satshakit/satshakit-M7/media/satshakit-M7-clock-config.png

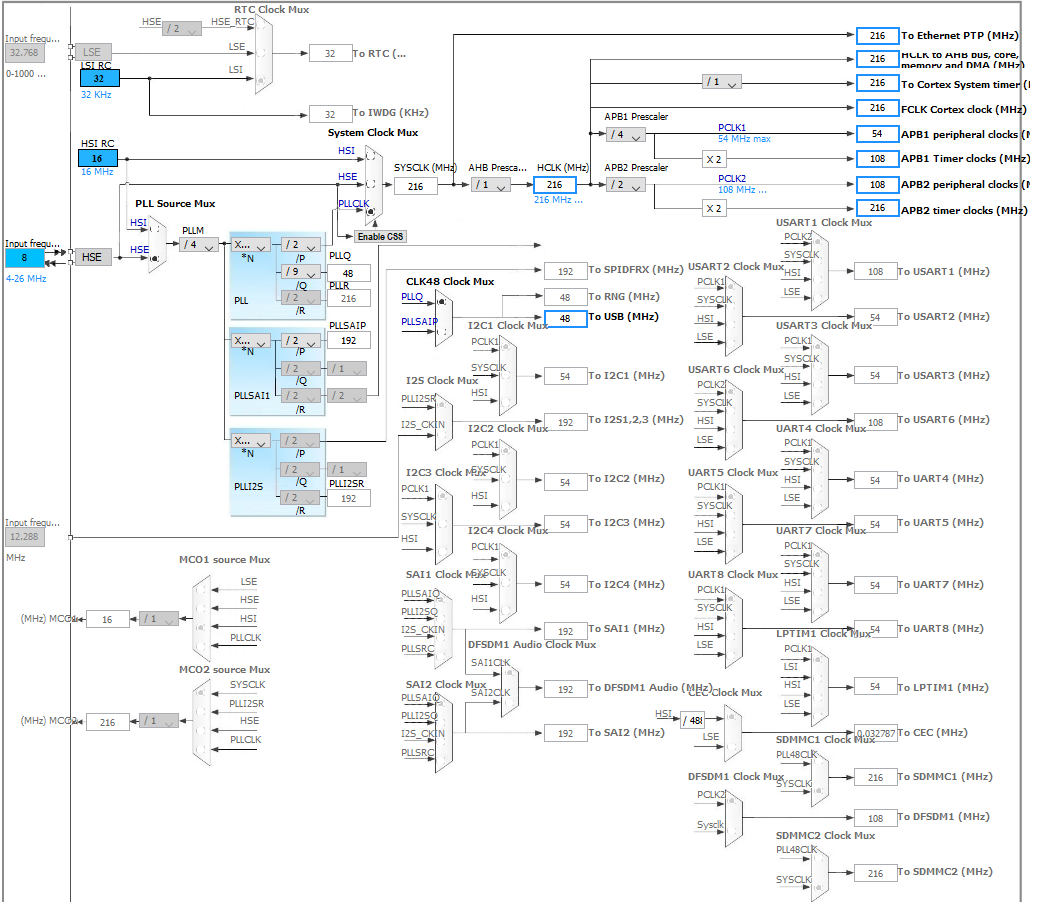
media/satshakit-M7-clock-config.png
