satshakit/satshakit-M7/media/satshakit-M7-cutout.png

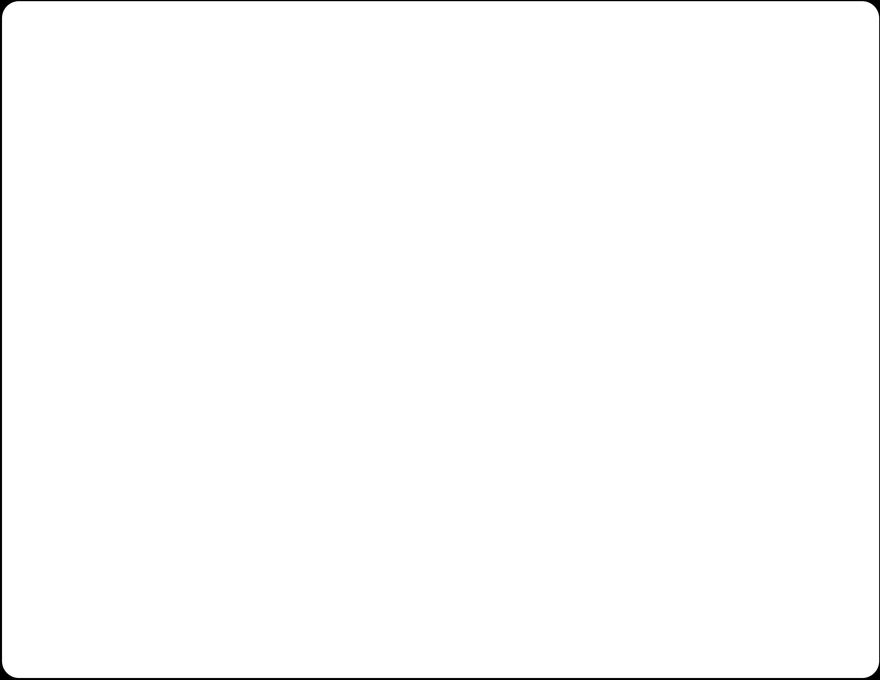
media/satshakit-M7-cutout.png
